Chrismettal/PiPLC/doc/PiPLC_labels_Top.png

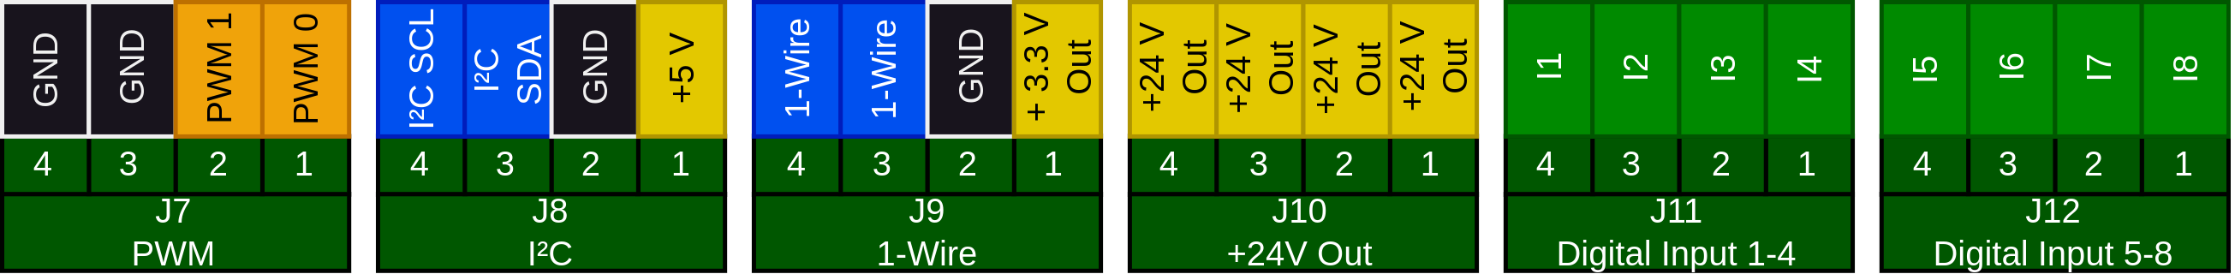
doc/PiPLC_labels_Top.png
